joshop/GuitarGame/firmware/include/its_tv_time.h

#pragma once
#include "music.h"
const AudioNote tvtime_left[] = {{391.995436, 12},
                                 {0, 12},
                                 {466.163762, 12},
                                 {0, 12},
                                 {523.251131, 18},
                                 {587.329536, 9},
                                 {0, 9},
                                 {698.456463, 6},
                                 {0, 6},
                                 {391.995436, 6},
                                 {0, 6},
                                 {391.995436, 6},
                                 {0, 6},
                                 {466.163762, 12},
                                 {0, 12},
                                 {554.365262, 18},
                                 {523.251131, 9},
                                 {0, 9},
                                 {466.163762, 12},
                                 {391.995436, 12},
                                 {0, 12},
                                 {466.163762, 12},
                                 {0, 12},
                                 {523.251131, 18},
                                 {587.329536, 9},
                                 {0, 9},
                                 {698.456463, 6},
                                 {0, 6},
                                 {391.995436, 6},
                                 {0, 6},
                                 {391.995436, 6},
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
    {1914, 2009, 1}, {2082, 0, 1},    {2094, 0, 0},    {2106, 0, 0},
    {2118, 0, 1},    {2130, 0, 1},    {2136, 0, 0},    {2148, 0, 0},
    {2154, 0, 1},    {2178, 0, 1},    {2190, 0, 1},    {2202, 0, 0},
    {2214, 0, 0},    {2220, 0, 1},    {2232, 0, 0},    {2244, 0, 0},
    {2256, 0, 1},    {2274, 0, 1},    {2286, 0, 0},    {2298, 0, 0},
    {2310, 0, 1},    {2322, 0, 1},    {2328, 0, 0},    {2340, 0, 0},
    {2346, 0, 1},    {2370, 0, 1},    {2382, 0, 1},    {2394, 0, 0},
    {2406, 0, 1},    {2412, 0, 0},    {2424, 0, 1},    {2436, 0, 0},
    {2448, 2477, 0}, {2502, 0, 1},    {2514, 0, 1},    {2526, 0, 0},
    {2532, 0, 1},    {2544, 2573, 0}, {2598, 0, 1},    {2610, 0, 1},
    {2622, 0, 0},    {2628, 2645, 1}, {2646, 2669, 0}, {2670, 0, 0},
    {2682, 2777, 1}, {2862, 0, 0},    {2874, 0, 0},    {2886, 0, 1},
    {2904, 0, 1},    {2922, 0, 0},    {2934, 0, 0},    {2952, 0, 1},
    {2970, 3029, 0}, {3054, 0, 0},    {3066, 0, 0},    {3078, 0, 1},
    {3096, 0, 1},    {3114, 0, 0},    {3126, 0, 0},    {3144, 3197, 1},
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
};
