joshop/GuitarGame/firmware/src/main/music.c

#include "music.h"
const uint8_t tvtime_dpcm[] = {
    0x96, 0x69, 0x99, 0x69, 0x99, 0x99, 0x96, 0x99, 0x99, 0x99, 0x99, 0x66,
    0x66, 0x99, 0x99, 0x92, 0x6a, 0xea, 0x51, 0x2a, 0xbd, 0x24, 0x9a, 0xbe,
    0x11, 0x2a, 0xbf, 0x01, 0x9a, 0xbb, 0x80, 0x5a, 0xee, 0x90, 0x16, 0xfe,
    0xa0, 0x56, 0xfd, 0x50, 0x55, 0xbf, 0x01, 0x1a, 0xbf, 0xc0, 0x16, 0xbf,
    0xc0, 0x96, 0xee, 0xc0, 0x1a, 0xee, 0xd0, 0x0a, 0xfe, 0xa0, 0x0a, 0xff,
    0x50, 0x1a, 0xff, 0x00, 0x2b, 0xbf, 0x80, 0x1b, 0xbf, 0x80, 0x0b, 0xfa,
    0xc0, 0x0e, 0xfe, 0x90, 0x1b, 0xfe, 0x00, 0x1b, 0xff, 0x00, 0x1b, 0xff,
    0x00, 0x1b, 0xfb, 0x40, 0x2b, 0xfd, 0x80, 0x1b, 0xfd, 0x40, 0x1b, 0xfe,
    0x00, 0x2f, 0xff, 0x00, 0x0f, 0xff, 0x00, 0x0b, 0xff, 0x00, 0x5b, 0xfd,
    0x00, 0x3b, 0xfd, 0x00, 0x2f, 0xfd, 0x00, 0x3f, 0xfc, 0x00, 0x6f, 0xf5,
    0x00, 0xef, 0xa5, 0x10, 0xfb, 0xb1, 0x44, 0xbb, 0x64, 0x55, 0xaa, 0xec,
    0x16, 0x96, 0xaa, 0x55, 0x5a, 0xbb, 0x51, 0x06, 0xbb, 0x95, 0x07, 0xfe,
    0xc0, 0x02, 0xff, 0x90, 0x0b, 0xff, 0x10, 0x0e, 0xff, 0x00, 0x0f, 0xfe,
    0x00, 0x2f, 0xfa, 0x00, 0xbf, 0xf4, 0x00, 0xff, 0xa0, 0x0a, 0xff, 0x80,
    0x0f, 0xfe, 0x00, 0x2f, 0xf1, 0x22, 0xea, 0xa1, 0x6b, 0x49, 0x9b, 0xe9,
    0x00, 0xfe, 0xa0, 0x0d, 0xff, 0x80, 0x0f, 0xfe, 0x00, 0x2f, 0xf8, 0x01,
    0xff, 0xa0, 0x06, 0xff, 0x00, 0x7f, 0xe4, 0x02, 0xff, 0x80, 0x1b, 0xfd,
    0x00, 0xbf, 0xc0, 0x0f, 0xfe, 0x40, 0xae, 0xd1, 0x26, 0xb9, 0x1a, 0xba,
    0x41, 0xae, 0xd0, 0x0a, 0xff, 0x81, 0x1f, 0xc4, 0x07, 0xff, 0x80, 0x2f,
    0xf8, 0x00, 0xff, 0x40, 0x1f, 0xfe, 0x00, 0xbe, 0xe0, 0x0b, 0xfe, 0x04,
    0x2f, 0xd1, 0x0a, 0xee, 0xc0, 0x6b, 0xf9, 0x04, 0x6e, 0x55, 0x6f, 0xea,
    0x45, 0x15, 0x54, 0xba, 0xaa, 0xa9, 0x51, 0x5a, 0xa9, 0x5b, 0xba, 0x41,
    0x5b, 0xd4, 0x42, 0xfe, 0xd0, 0x6f, 0x58, 0x05, 0x6f, 0x84, 0xeb, 0xf0,
    0x11, 0xfd, 0x01, 0x6f, 0xf4, 0x03, 0xf9, 0x80, 0x3f, 0xf4, 0x1a, 0xbe,
    0x01, 0x5b, 0xd1, 0x16, 0xfc, 0x10, 0xbf, 0xa8, 0x06, 0xff, 0x91, 0x07,
    0xf4, 0x44, 0x66, 0xea, 0x6f, 0x80, 0x4b, 0xea, 0x50, 0xff, 0x64, 0x0a,
    0xbf, 0x01, 0xab, 0x81, 0x2b, 0xfc, 0x11, 0x7f, 0x01, 0x1b, 0xff, 0x44,
    0xe9, 0x10, 0x3b, 0xbc, 0x0b, 0xba, 0x91, 0x26, 0xf1, 0x2a, 0xa9, 0x9a,
    0xbe, 0x80, 0x16, 0xa9, 0x92, 0xbf, 0xe8, 0x11, 0x59, 0x57, 0xed, 0xa5,
    0x45, 0x94, 0x1a, 0xfb, 0xa5, 0x0b, 0xa0, 0x46, 0xbb, 0xf4, 0x2f, 0xb9,
    0x00, 0x1f, 0xe0, 0x57, 0xfe, 0xc0, 0xad, 0x00, 0x4e, 0xbf, 0x93, 0xaa,
    0x80, 0x2d, 0x9a, 0xea, 0xee, 0x40, 0x06, 0xda, 0xbe, 0xfc, 0x00, 0x2f,
    0xb9, 0x0b, 0xe4, 0x41, 0xae, 0xe4, 0x1b, 0x55, 0x55, 0xaf, 0x80, 0xfe,
    0xa5, 0x44, 0xbf, 0x15, 0x25, 0x65, 0x06, 0xef, 0xa0, 0xbb, 0xa5, 0x25,
    0x6b, 0x55, 0xaa, 0x91, 0x7f, 0x60, 0x02, 0xaa, 0xbb, 0xfc, 0x91, 0x10,
    0x55, 0x9f, 0xfb, 0x41, 0x54, 0xa5, 0x6e, 0xaa, 0xaa, 0x80, 0x16, 0xfa,
    0x5f, 0xe1, 0x00, 0x3b, 0xf5, 0x6b, 0xb8, 0x00, 0x2a, 0xbb, 0xfa, 0x99,
    0x6a, 0x04, 0x1a, 0xea, 0xb8, 0x03, 0xff, 0x40, 0x0b, 0xf9, 0x84, 0x7f,
    0xf9, 0x11, 0x45, 0xad, 0x52, 0x5a, 0xba, 0x94, 0x1f, 0xea, 0x94, 0x04,
    0x6f, 0xfd, 0x00, 0xfb, 0xc0, 0x2e, 0x5a, 0xae, 0x84, 0x96, 0xf4, 0x11,
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
