joshop/GuitarGame/firmware/include/raise_up_your_bat.h

#include "music.h"
const Note song1[] = {
    {150, 0, 0},     {161, 0, 1},     {176, 193, 1},   {197, 0, 1},
    {213, 0, 0},     {229, 0, 0},     {244, 0, 1},     {260, 0, 0},
    {275, 0, 1},     {286, 0, 0},     {302, 0, 1},     {322, 0, 1},
    {338, 0, 0},     {354, 0, 0},     {364, 416, 1},   {442, 0, 1},
    {463, 0, 1},     {474, 0, 0},     {490, 0, 1},     {505, 0, 1},
    {510, 0, 0},     {520, 0, 1},     {542, 0, 1},     {557, 635, 0},
    {651, 0, 0},     {662, 0, 1},     {674, 694, 1},   {698, 0, 0},
    {714, 0, 0},     {730, 0, 1},     {745, 0, 0},     {761, 0, 1},
    {776, 0, 1},     {787, 0, 0},     {802, 820, 1},   {823, 0, 0},
    {839, 0, 0},     {850, 0, 0},     {865, 933, 1},   {943, 0, 0},
    {964, 0, 1},     {974, 0, 0},     {988, 0, 1},     {1011, 0, 0},
    {1027, 0, 1},    {1037, 0, 1},    {1050, 1160, 1}, {1194, 0, 1},
    {1214, 0, 1},    {1225, 0, 0},    {1235, 1250, 1}, {1254, 0, 0},
    {1277, 0, 0},    {1288, 0, 1},    {1301, 1418, 1}, {1434, 0, 0},
    {1528, 0, 0},    {1559, 0, 1},    {1622, 0, 1},    {1684, 0, 1},
    {1747, 0, 1},    {1794, 0, 0},    {1810, 0, 1},    {1856, 0, 1},
    {1872, 0, 1},    {1934, 0, 1},    {1982, 0, 0},    {1997, 0, 1},
    {2044, 0, 0},    {2060, 0, 0},    {2091, 0, 1},    {2122, 0, 0},
    {2170, 0, 0},    {2185, 0, 1},    {2201, 0, 1},    {2216, 0, 1},
    {2232, 0, 0},    {2248, 0, 1},    {2279, 0, 0},    {2310, 0, 1},
    {2342, 0, 1},    {2373, 0, 0},    {2420, 0, 0},    {2435, 0, 1},
    {2467, 0, 1},    {2482, 0, 0},    {2498, 0, 1},    {2530, 0, 0},
    {2561, 2592, 1}, {2686, 0, 1},    {2733, 0, 0},    {2749, 0, 0},
    {2764, 0, 1},    {2780, 0, 1},    {2795, 0, 0},    {2811, 0, 1},
    {2842, 0, 1},    {2858, 2905, 0}, {2921, 0, 0},    {2936, 0, 1},
    {2952, 0, 1},    {2968, 0, 0},    {2983, 0, 0},    {2999, 0, 1},
    {3022, 0, 0},    {3046, 0, 1},    {3062, 3093, 0}, {3109, 0, 0},
    {3124, 0, 1},    {3187, 0, 0},    {3234, 0, 0},    {3250, 0, 0},
    {3265, 0, 1},    {3281, 0, 0},    {3296, 0, 1},    {3312, 0, 1},
    {3335, 0, 1},    {3359, 3406, 1}, {3422, 0, 1},    {3437, 0, 0},
    {3453, 0, 0},    {3469, 0, 0},    {3484, 0, 1},    {3500, 0, 1},
    {3515, 0, 0},    {3531, 0, 1},    {3547, 0, 0},    {3562, 3594, 0},
    {3610, 0, 1},    {3625, 0, 0},    {3672, 0, 0},    {3688, 0, 1},
    {3703, 0, 1},    {3719, 0, 0},    {3734, 0, 0},    {3750, 0, 1},
    {3766, 0, 0},    {3782, 0, 1},    {3797, 0, 0},    {3813, 3844, 1},
    {3860, 0, 0},    {3875, 0, 1},    {3938, 0, 0},    {3949, 0, 1},
    {3954, 0, 0},    {3964, 0, 1},    {3970, 0, 0},    {3980, 0, 1},
    {3985, 0, 0},    {3995, 0, 1},    {4001, 0, 0},    {4011, 0, 1},
    {4016, 0, 0},    {4027, 0, 0},    {4042, 0, 0},    {4058, 0, 0},
    {4063, 4083, 1}, {4091, 4106, 1}, {4110, 0, 0},    {4126, 0, 1},
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
};
